pmandes/zx-spectrum-issue6a-replica/images/assembled1.jpg

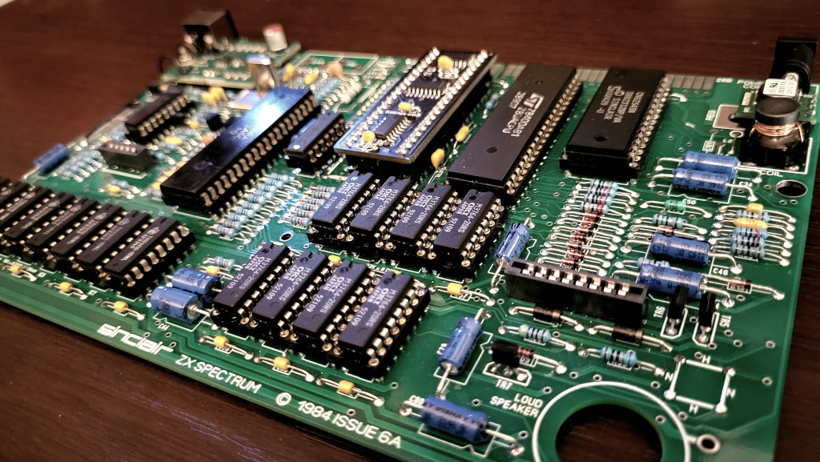
images/assembled1.jpg
