pmandes/zx-spectrum-issue6a-replica/images/assembled2.jpg

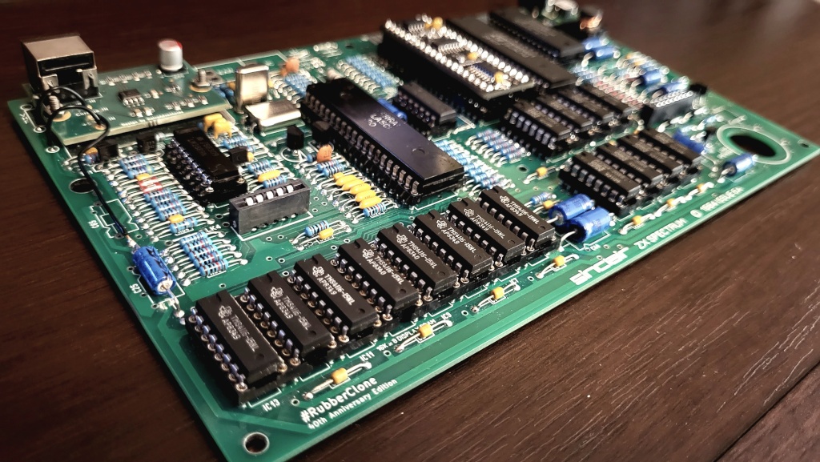
images/assembled2.jpg
